kholia/Adjustable-Load-v1.1/datasheets/22uF information.png

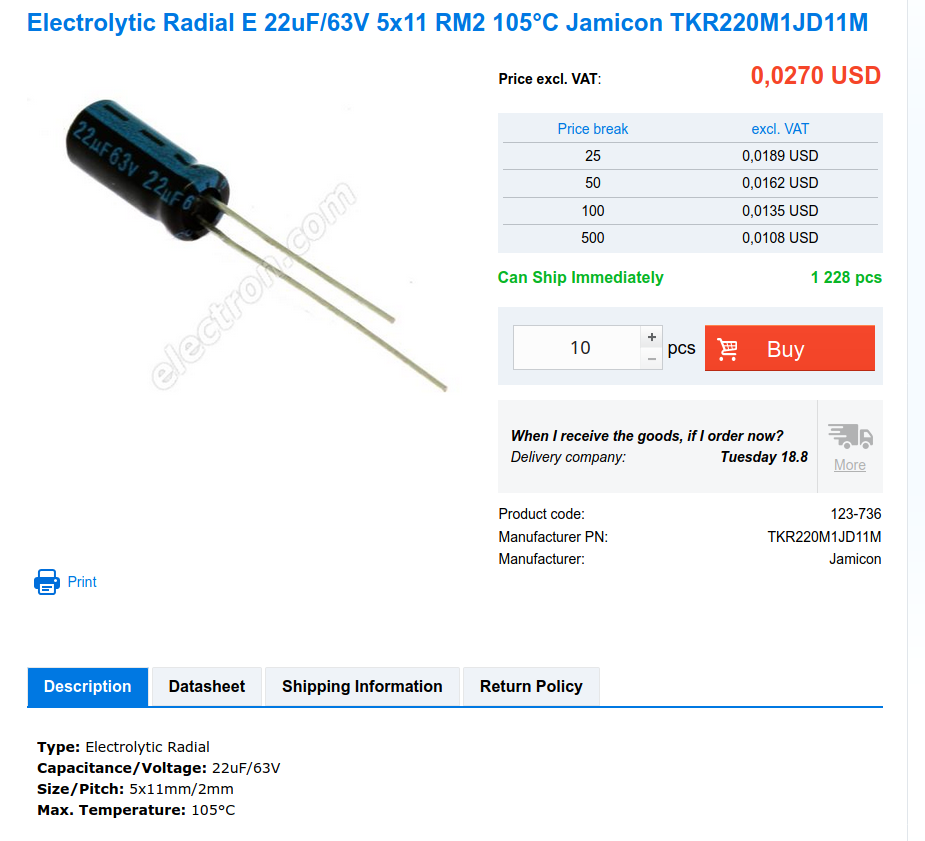
datasheets/22uF information.png
