kholia/Adjustable-Load-v1.1/datasheets/2020-08-14 23.40.08.jpg

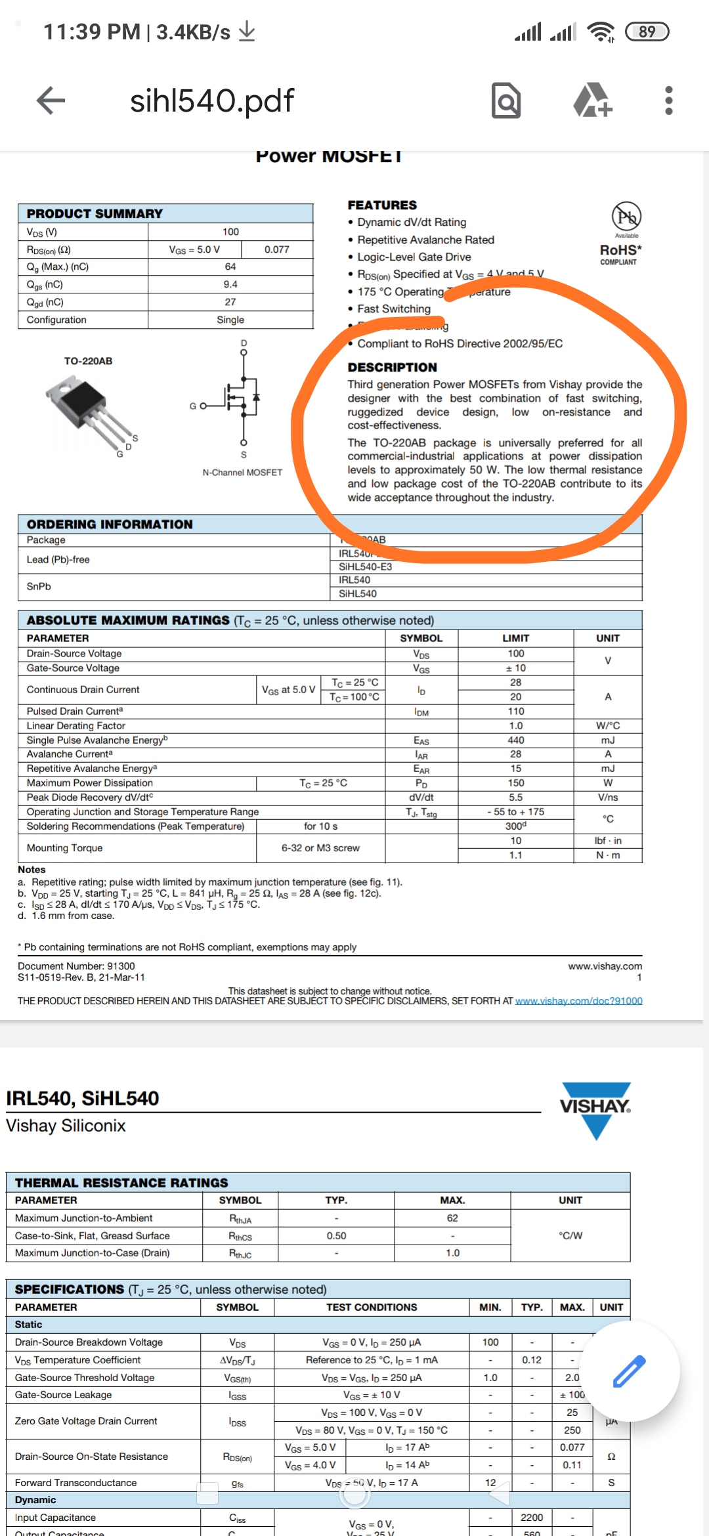
datasheets/2020-08-14 23.40.08.jpg
