kholia/Adjustable-Load-v1.1/datasheets/LM27222 driver safety feature.png

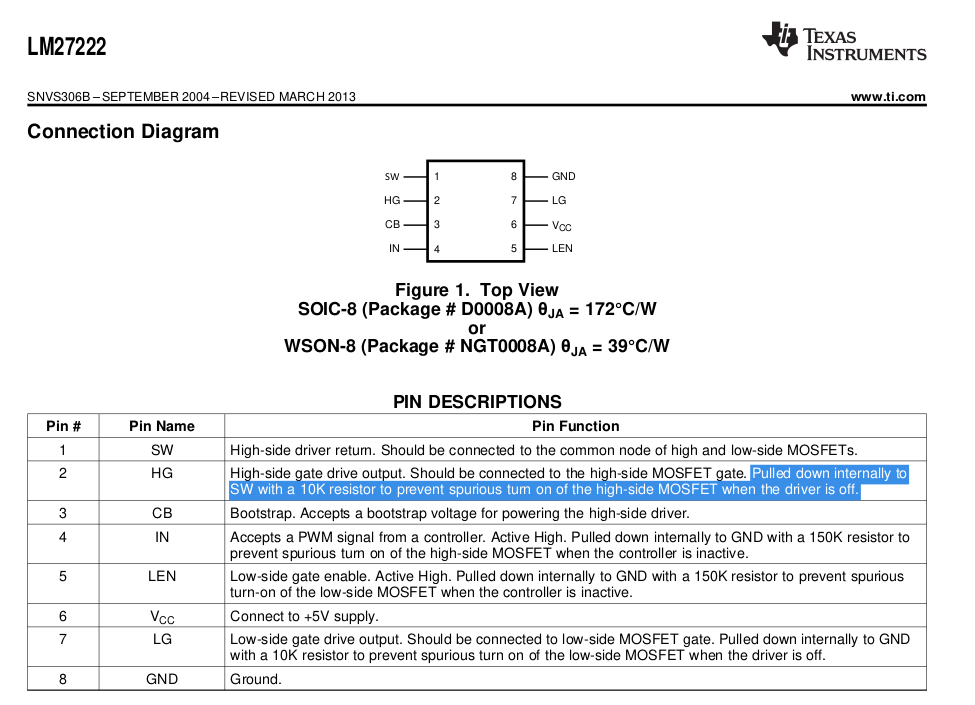
datasheets/LM27222 driver safety feature.png
