kholia/Adjustable-Load-v1.1/images/5a-current-sensor-module-acs712 - 2.jpg

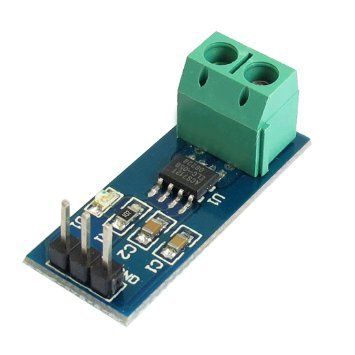
images/5a-current-sensor-module-acs712 - 2.jpg
