kholia/Adjustable-Load-v1.1/images/ACS712-Current-Sensor-Circuit.png

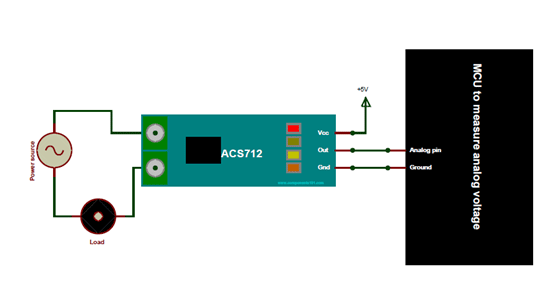
images/ACS712-Current-Sensor-Circuit.png
