kholia/Adjustable-Load-v1.1/images/I2C module closeup.jpg

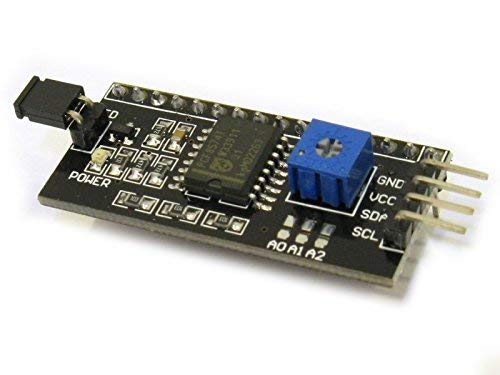
images/I2C module closeup.jpg
