kholia/Adjustable-Load-v1.1/images/I2C-16x02-Serial-LCD-02.jpg

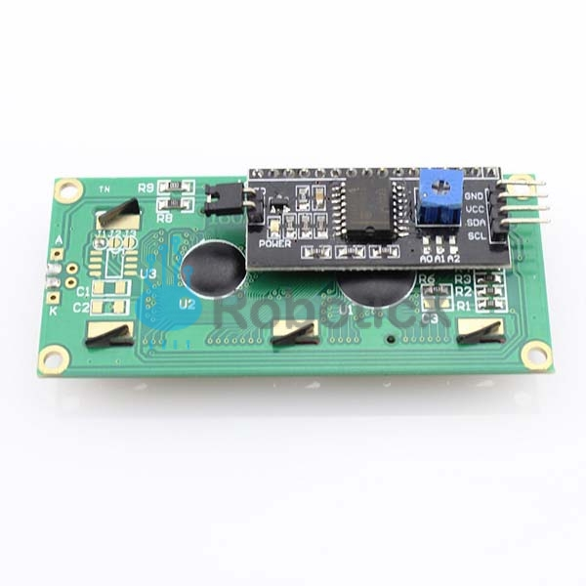
images/I2C-16x02-Serial-LCD-02.jpg
