kholia/Adjustable-Load-v1.1/images/KY-040 Rotary Encoder Module.jpg

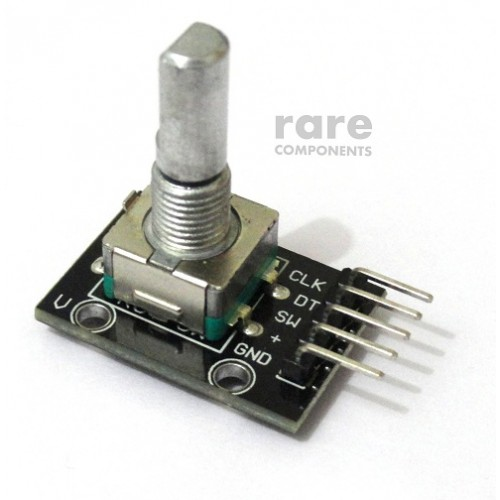
images/KY-040 Rotary Encoder Module.jpg
