kholia/Adjustable-Load-v1.1/images/MOSFET symbols.png

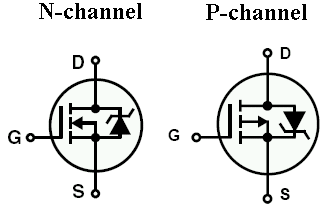
images/MOSFET symbols.png
