kholia/Adjustable-Load-v1.1/images/Safety Tweak - 150k resistor in IRFZ gate control is for the MOSFET protection during the startup.jpg

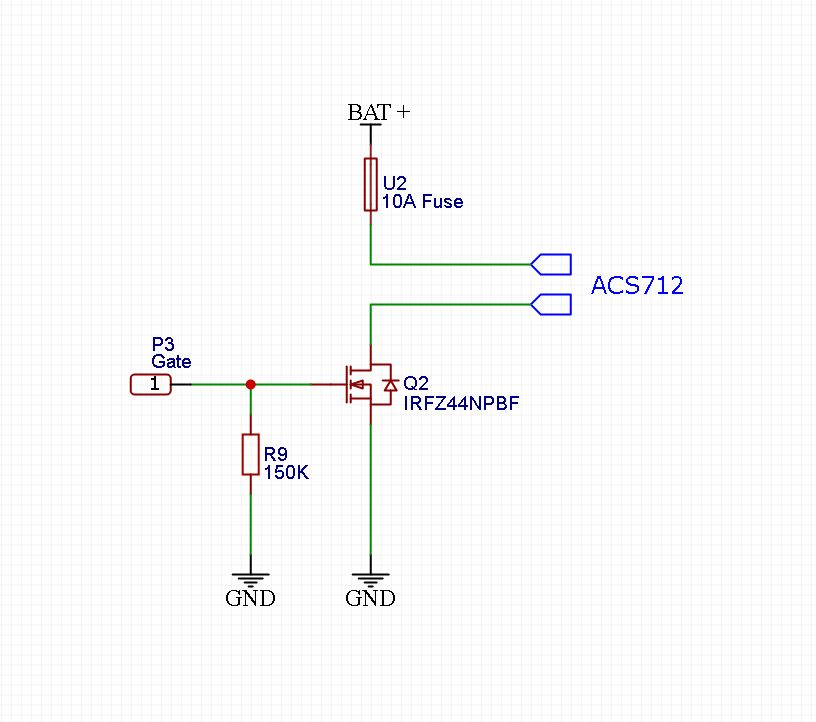
images/Safety Tweak - 150k resistor in IRFZ gate control is for the MOSFET protection during the startup.jpg
