kholia/Adjustable-Load-v1.1/BOM My.png

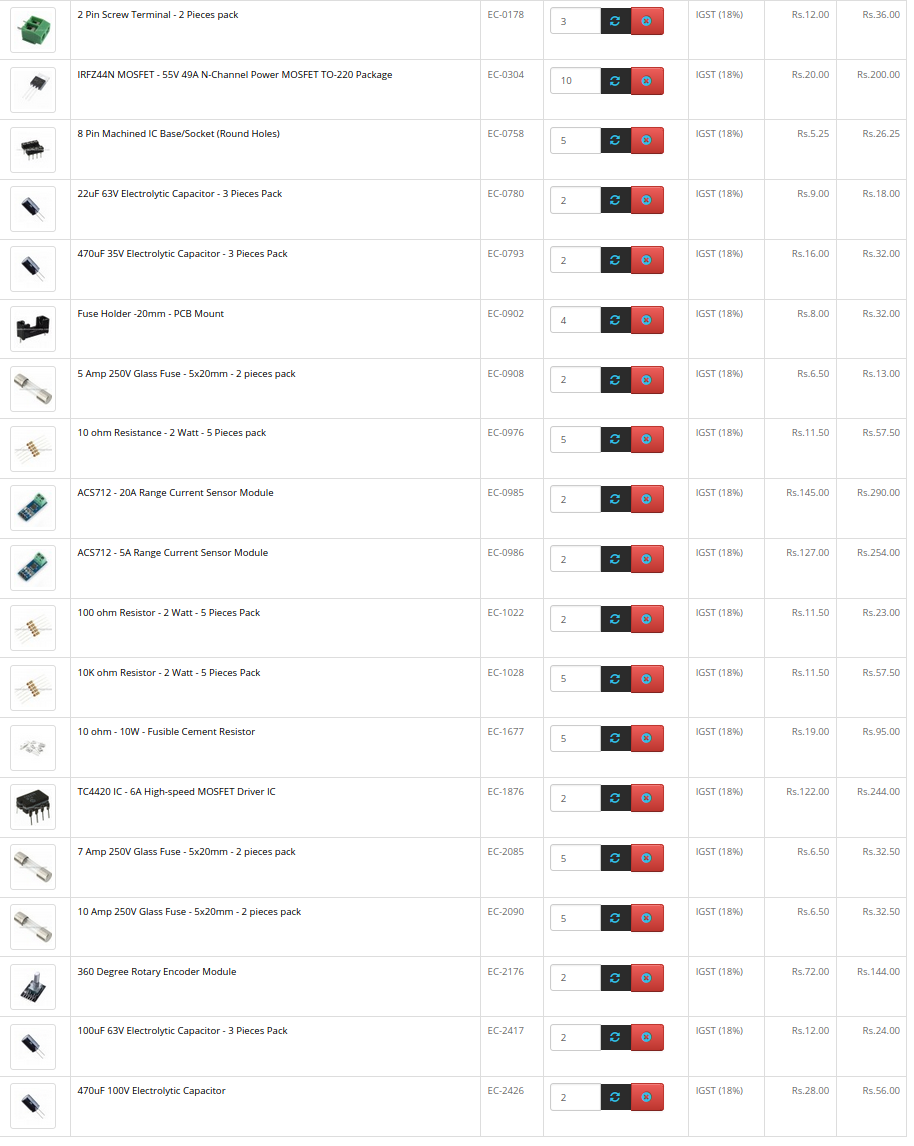
BOM My.png
