kholia/Adjustable-Load-v1.1/GreatScott-Build-Images/1.jpeg

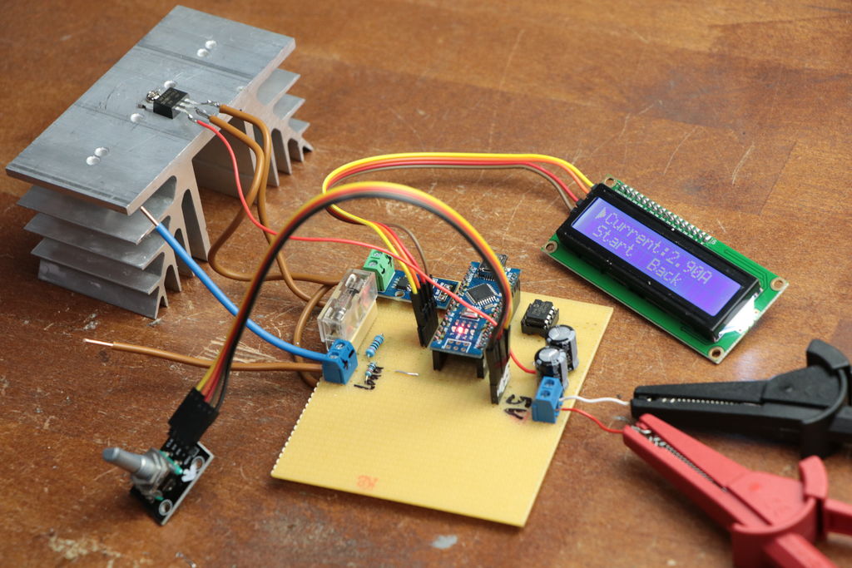
GreatScott-Build-Images/1.jpeg
