kholia/Adjustable-Load-v1.1/GreatScott-Build-Images/2.jpg

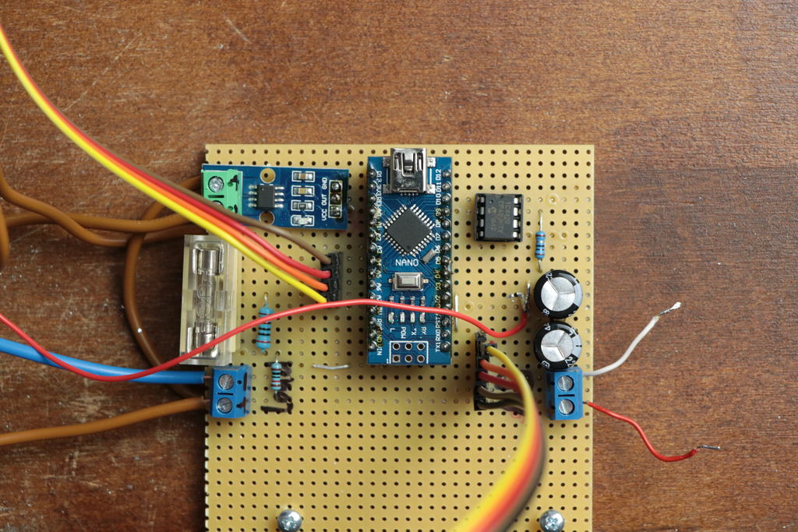
GreatScott-Build-Images/2.jpg
