kholia/Adjustable-Load-v1.1/GreatScott-Build-Images/3.jpg

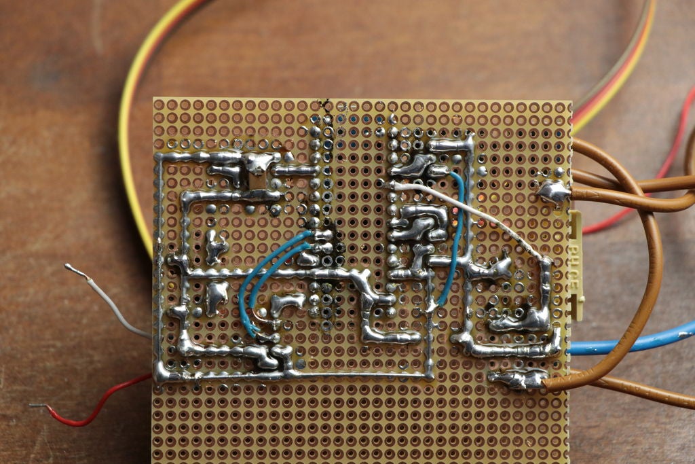
GreatScott-Build-Images/3.jpg
